not-sample-text/Proiect-Licenta/hardware/pcb/Imports/3d/Bottom-3D/SK6812MINI-E v1.step

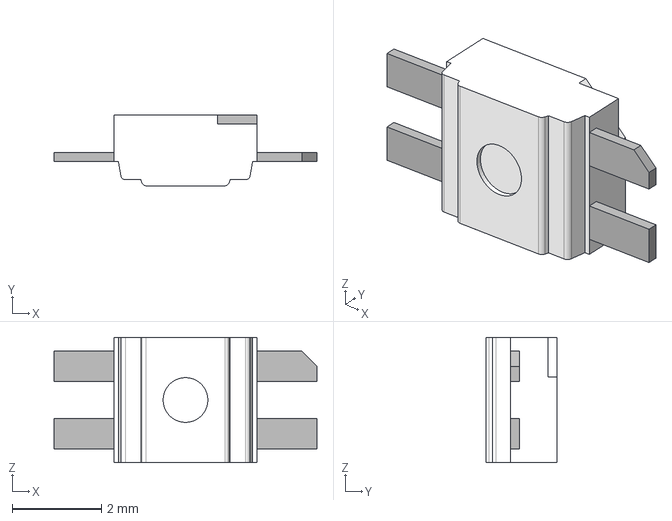
[picture p24: CAD file, 2025-07-28]
hardware/pcb/Imports/3d/Bottom-3D/SK6812MINI-E v1.step
5.88 x 1.58 x 2.80 mm
