not-sample-text/Proiect-Licenta/hardware/pcb/Imports/3d/Top-3D/MX_PCB.step

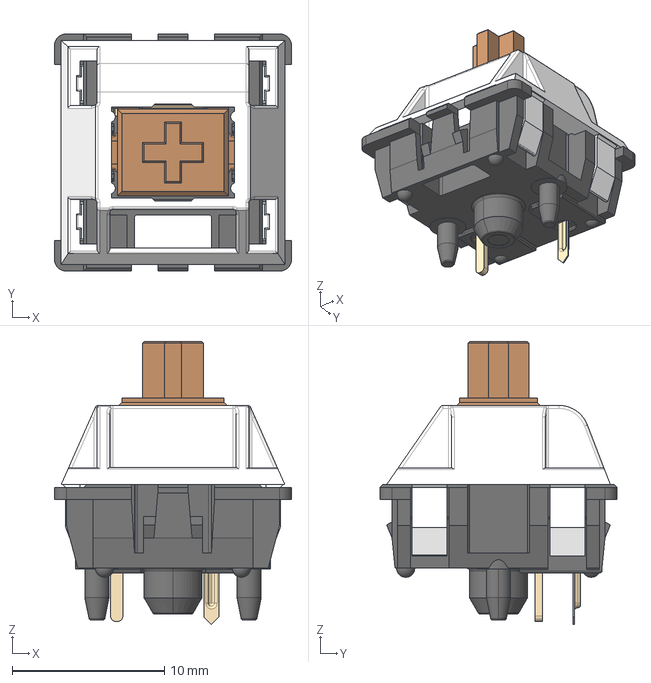
[picture p25: CAD file, 2025-07-28]
hardware/pcb/Imports/3d/Top-3D/MX_PCB.step
15.6 x 15.6 x 18.6 mm
