not-sample-text/Proiect-Licenta/hardware/pcb/Imports/3d/Bottom-3D/TPS22918DBVR.stp

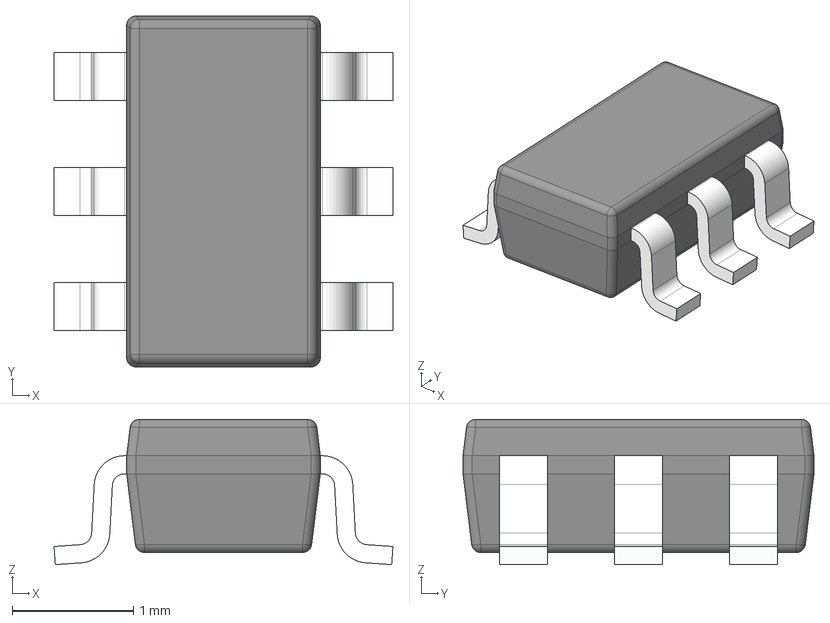
[picture p26: CAD file, 2025-12-25]
hardware/pcb/Imports/3d/Bottom-3D/TPS22918DBVR.stp
2.80 x 2.90 x 1.20 mm
BODY-SOT
LEAD-SOT x 6
