not-sample-text/Proiect-Licenta/hardware/pcb/Imports/3d/Top-3D/PG151101S11.step

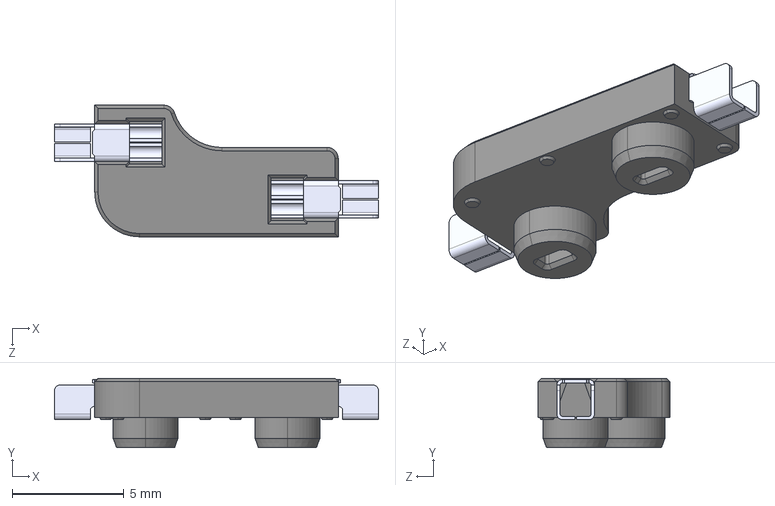
[picture p27: CAD file, 2025-07-28]
hardware/pcb/Imports/3d/Top-3D/PG151101S11.step
14.5 x 3.10 x 5.89 mm
